maniekx86/M8SBC-486/pcb/cpu.kicad_sch

## KiCad design pcb/cpu.kicad_sch (2025-09-24)

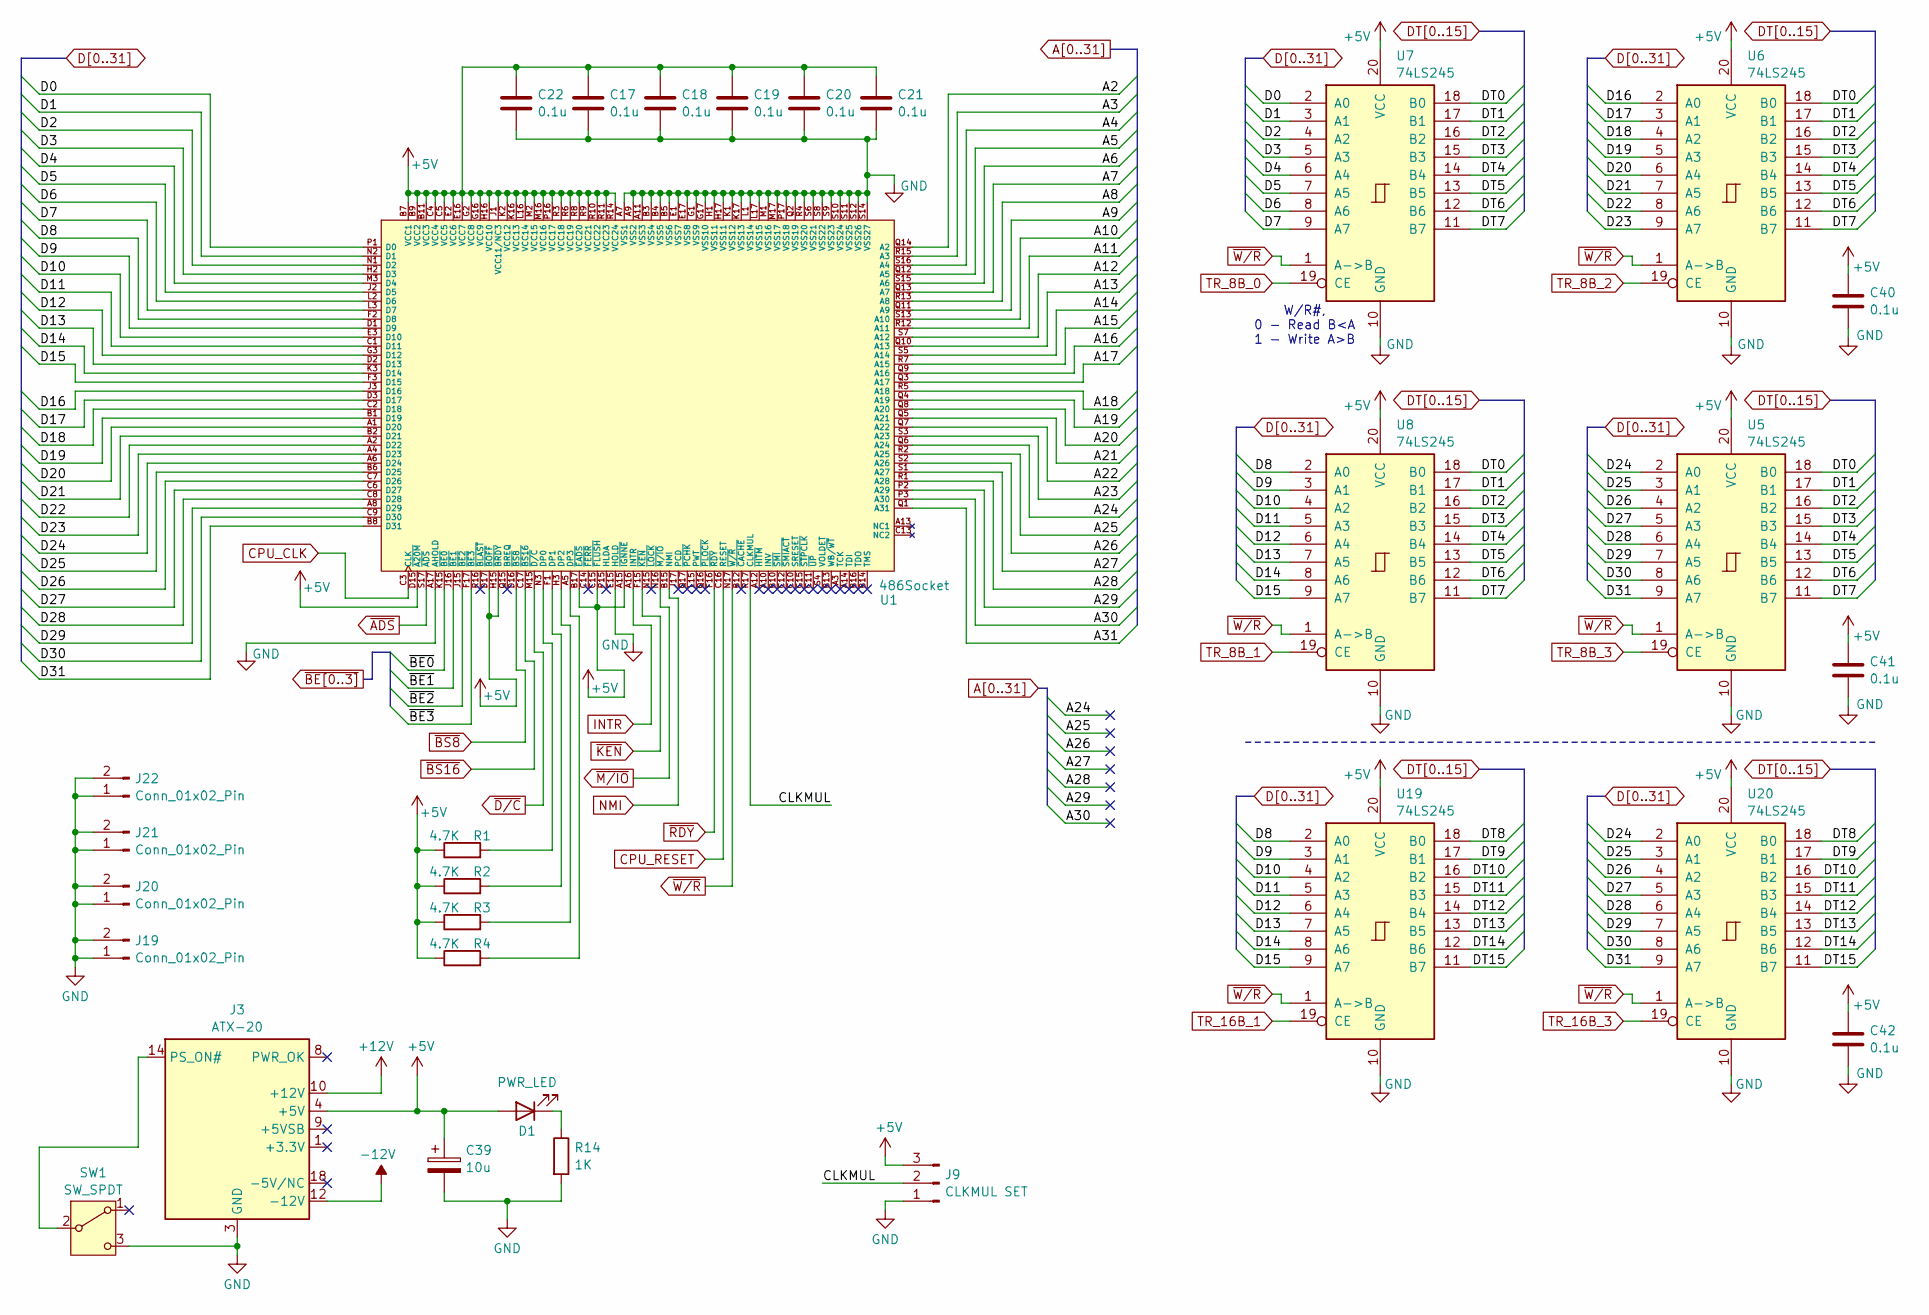
[picture p5: schematic cpu.kicad_sch]

Parts:
C17, C18, C19, C20, C21, C22, C40, C41, C42: 0.1u; C_0805_2012Metric_Pad1.18x1.45mm_HandSolder
C39: 10u; CP_Radial_D5.0mm_P2.50mm
D1: PWR_LED; LED_D4.0mm
J3: ATX-20; Molex_Mini-Fit_Jr_5566-20A_2x10_P4.20mm_Vertical
J9: CLKMUL SET; PinHeader_1x03_P2.54mm_Vertical
J19, J20, J21, J22: Conn_01x02_Pin; PinHeader_1x02_P2.54mm_Vertical
R1, R2, R3, R4: 4.7K; R_0805_2012Metric_Pad1.20x1.40mm_HandSolder
R14: 1K; R_0805_2012Metric_Pad1.20x1.40mm_HandSolder
SW1: SW_SPDT; PinHeader_1x03_P2.54mm_Vertical
U1: 486Socket
U5, U6, U7, U8, U19, U20: 74LS245; SOP-20_7.5x12.8mm_P1.27mm

Connections:
+5V: C17.2, C18.2, C19.2, C20.2, C21.2, C22.2, C39.1, C40.2, C41.2, C42.2, D1.2 (A), J3.4 (+5V), J3.6 (+5V), J3.19 (+5V), J3.20 (+5V), J9.3, R1.1, R2.1, R3.1, R4.1, U1.A15 (~IGNNE), U1.B7 (VCC1), U1.B9 (VCC2), U1.B11 (VCC3), U1.B17 (~EADS), U1.C4 (VCC4), U1.C5 (VCC5), U1.C15 (~FLUSH), U1.D15 (~A20M), U1.D17 (~BOFF), U1.E2 (VCC6), U1.E16 (VCC7), U1.G2 (VCC8), U1.G16 (VCC9), U1.H15 (~BRDY), U1.H16 (VCC10), U1.J1 (VCC11/NC3), U1.K2 (VCC12), U1.K16 (VCC13), U1.L16 (VCC14), U1.M2 (VCC15), U1.M16 (VCC16), U1.P16 (VCC17), U1.R3 (VCC18), U1.R6 (VCC19), U1.R8 (VCC20), U1.R9 (VCC21), U1.R10 (VCC22), U1.R11 (VCC23), U1.R14 (VCC24), U5.20 (VCC), U6.20 (VCC), U7.20 (VCC), U8.20 (VCC), U19.20 (VCC), U20.20 (VCC)
+12V: J3.10 (+12V)
-12V: J3.12 (-12V)
A2: U1.Q14 (A2)
A3: U1.R15 (A3)
A4: U1.S16 (A4)
A5: U1.Q12 (A5)
A6: U1.S15 (A6)
A7: U1.Q13 (A7)
A8: U1.R13 (A8)
A9: U1.Q11 (A9)
A10: U1.S13 (A10)
A11: U1.R12 (A11)
A12: U1.S7 (A12)
A13: U1.Q10 (A13)
A14: U1.S5 (A14)
A15: U1.R7 (A15)
A16: U1.Q9 (A16)
A17: U1.Q3 (A17)
A18: U1.R5 (A18)
A19: U1.Q4 (A19)
A20: U1.Q8 (A20)
A21: U1.Q5 (A21)
A22: U1.Q7 (A22)
A23: U1.S3 (A23)
A24: U1.Q6 (A24)
A25: U1.R2 (A25)
A26: U1.S2 (A26)
A27: U1.S1 (A27)
A28: U1.R1 (A28)
A29: U1.P2 (A29)
A30: U1.P3 (A30)
A31: U1.Q1 (A31)
CLKMUL: J9.2, U1.R17 (CLKMUL)
CPU_CLK: U1.C3 (CLK)
CPU_RESET: U1.C16 (RESET)
D0: U1.P1 (D0), U7.2 (A0)
D1: U1.N2 (D1), U7.3 (A1)
D2: U1.N1 (D2), U7.4 (A2)
D3: U1.H2 (D3), U7.5 (A3)
D4: U1.M3 (D4), U7.6 (A4)
D5: U1.J2 (D5), U7.7 (A5)
D6: U1.L2 (D6), U7.8 (A6)
D7: U1.L3 (D7), U7.9 (A7)
D8: U1.F2 (D8), U8.2 (A0), U19.2 (A0)
D9: U1.D1 (D9), U8.3 (A1), U19.3 (A1)
D10: U1.E3 (D10), U8.4 (A2), U19.4 (A2)
D11: U1.C1 (D11), U8.5 (A3), U19.5 (A3)
D12: U1.G3 (D12), U8.6 (A4), U19.6 (A4)
D13: U1.D2 (D13), U8.7 (A5), U19.7 (A5)
D14: U1.K3 (D14), U8.8 (A6), U19.8 (A6)
D15: U1.F3 (D15), U8.9 (A7), U19.9 (A7)
D16: U1.J3 (D16), U6.2 (A0)
D17: U1.D3 (D17), U6.3 (A1)
D18: U1.C2 (D18), U6.4 (A2)
D19: U1.B1 (D19), U6.5 (A3)
D20: U1.A1 (D20), U6.6 (A4)
D21: U1.B2 (D21), U6.7 (A5)
D22: U1.A2 (D22), U6.8 (A6)
D23: U1.A4 (D23), U6.9 (A7)
D24: U1.A6 (D24), U5.2 (A0), U20.2 (A0)
D25: U1.B6 (D25), U5.3 (A1), U20.3 (A1)
D26: U1.C7 (D26), U5.4 (A2), U20.4 (A2)
D27: U1.C6 (D27), U5.5 (A3), U20.5 (A3)
D28: U1.C8 (D28), U5.6 (A4), U20.6 (A4)
D29: U1.A8 (D29), U5.7 (A5), U20.7 (A5)
D30: U1.C9 (D30), U5.8 (A6), U20.8 (A6)
D31: U1.B8 (D31), U5.9 (A7), U20.9 (A7)
DT0: U5.18 (B0), U6.18 (B0), U7.18 (B0), U8.18 (B0)
DT1: U5.17 (B1), U6.17 (B1), U7.17 (B1), U8.17 (B1)
DT2: U5.16 (B2), U6.16 (B2), U7.16 (B2), U8.16 (B2)
DT3: U5.15 (B3), U6.15 (B3), U7.15 (B3), U8.15 (B3)
DT4: U5.14 (B4), U6.14 (B4), U7.14 (B4), U8.14 (B4)
DT5: U5.13 (B5), U6.13 (B5), U7.13 (B5), U8.13 (B5)
DT6: U5.12 (B6), U6.12 (B6), U7.12 (B6), U8.12 (B6)
DT7: U5.11 (B7), U6.11 (B7), U7.11 (B7), U8.11 (B7)
DT8: U19.18 (B0), U20.18 (B0)
DT9: U19.17 (B1), U20.17 (B1)
DT10: U19.16 (B2), U20.16 (B2)
DT11: U19.15 (B3), U20.15 (B3)
DT12: U19.14 (B4), U20.14 (B4)
DT13: U19.13 (B5), U20.13 (B5)
DT14: U19.12 (B6), U20.12 (B6)
DT15: U19.11 (B7), U20.11 (B7)
GND: C17.1, C18.1, C19.1, C20.1, C21.1, C22.1, C39.2, C40.1, C41.1, C42.1, J3.3 (GND), J3.5 (GND), J3.7 (GND), J3.13 (GND), J3.15 (GND), J3.16 (GND), J3.17 (GND), J9.1, J19.1, J19.2, J20.1, J20.2, J21.1, J21.2, J22.1, J22.2, R14.2, SW1.3 (C), U1.A7 (VSS1), U1.A9 (VSS2), U1.A11 (VSS3), U1.A17 (AHOLD), U1.B3 (VSS4), U1.B4 (VSS5), U1.B5 (VSS6), U1.E1 (VSS7), U1.E15 (HOLD), U1.E17 (VSS8), U1.G1 (VSS9), U1.G17 (VSS10), U1.H1 (VSS11), U1.H17 (VSS11), U1.K1 (VSS12), U1.K17 (VSS13), U1.L1 (VSS14), U1.L17 (VSS15), U1.M1 (VSS16), U1.M17 (VSS17), U1.P17 (VSS18), U1.Q2 (VSS19), U1.R4 (VSS20), U1.S6 (VSS21), U1.S8 (VSS22), U1.S9 (VSS23), U1.S10 (VSS24), U1.S11 (VSS25), U1.S12 (VSS26), U1.S14 (VSS27), U5.10 (GND), U6.10 (GND), U7.10 (GND), U8.10 (GND), U19.10 (GND), U20.10 (GND)
INTR: U1.A16 (INTR)
NMI: U1.B15 (NMI)
unnamed: D1.1 (K), R14.1
unnamed: J3.1 (+3.3V), J3.2 (+3.3V), J3.11 (+3.3V)
unnamed: J3.14 (PS_ON#), SW1.2 (B)
unnamed: R1.2, U1.N3 (DP0)
unnamed: R2.2, U1.F1 (DP1)
unnamed: R3.2, U1.H3 (DP2)
unnamed: R4.2, U1.A5 (DP3)
TR_8B_0: U7.19 (CE)
TR_8B_1: U8.19 (CE)
TR_8B_2: U6.19 (CE)
TR_8B_3: U5.19 (CE)
TR_16B_1: U19.19 (CE)
TR_16B_3: U20.19 (CE)
~ADS: U1.S17 (~ADS)
~BE0: U1.K15 (~BE0)
~BE1: U1.J16 (~BE1)
~BE2: U1.J15 (~BE2)
~BE3: U1.F17 (~BE3)
~BS8: U1.D16 (~BS8)
~BS16: U1.C17 (~BS16)
~D/C: U1.M15 (~D/C)
~KEN: U1.F15 (~KEN)
~M/IO: U1.N16 (~M/IO)
~RDY: U1.F16 (~RDY)
~W/R: U1.N17 (~W/R), U5.1 (A->B), U6.1 (A->B), U7.1 (A->B), U8.1 (A->B), U19.1 (A->B), U20.1 (A->B)

Notes on the sheet:
W/R#, 0 - Read B<A 1 - Write A>B
