maniekx86/M8SBC-486/pcb/fpga.kicad_sch

## KiCad design pcb/fpga.kicad_sch (2025-09-24)

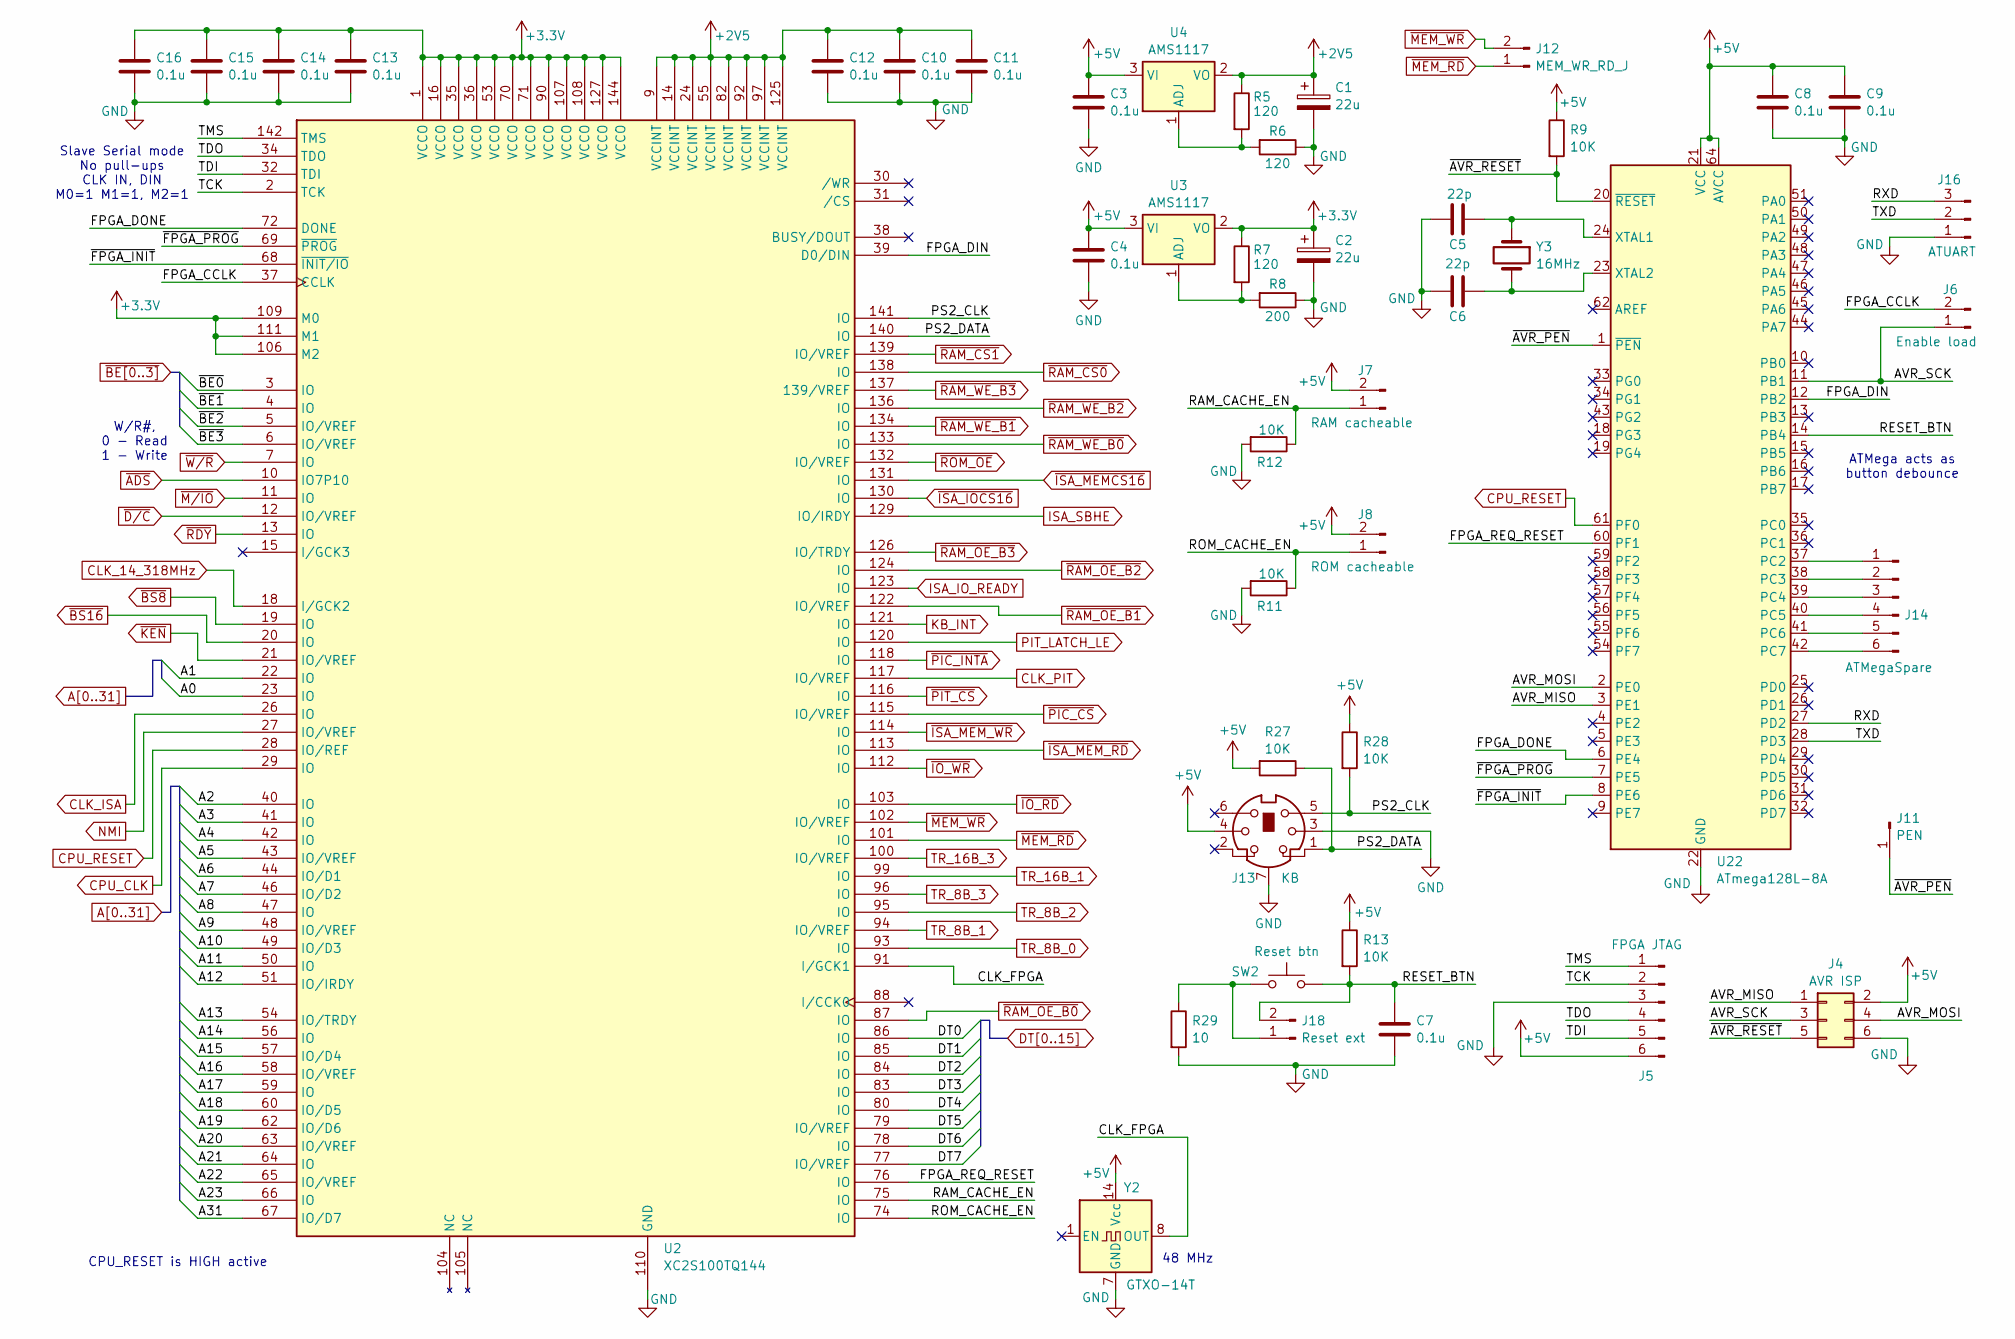
[picture p6: schematic fpga.kicad_sch]

Parts:
C1, C2: 22u; CP_Radial_D5.0mm_P2.50mm
C3, C4, C7, C8, C9, C10, C11, C12, C13, C14, C15, C16: 0.1u; C_0805_2012Metric_Pad1.18x1.45mm_HandSolder
C5, C6: 22p; C_0805_2012Metric_Pad1.18x1.45mm_HandSolder
J4: AVR ISP; PinHeader_2x03_P2.54mm_Vertical
J5: FPGA JTAG; PinHeader_1x06_P2.54mm_Vertical
J6: Enable load; PinHeader_1x02_P2.54mm_Vertical
J7: RAM cacheable; PinHeader_1x02_P2.54mm_Vertical
J8: ROM cacheable; PinHeader_1x02_P2.54mm_Vertical
J11: PEN; PinHeader_1x01_P2.54mm_Vertical
J12: MEM_WR_RD_J; PinHeader_1x02_P2.54mm_Vertical
J13: KB; Connector_Mini-DIN_Female_6Pin_2rows
J14: ATMegaSpare; PinHeader_1x06_P2.54mm_Vertical
J16: ATUART; PinHeader_1x03_P2.54mm_Vertical
J18: Reset ext; PinHeader_1x02_P2.54mm_Vertical
R5, R6, R7: 120; R_0805_2012Metric_Pad1.20x1.40mm_HandSolder
R8: 200; R_0805_2012Metric_Pad1.20x1.40mm_HandSolder
R9, R11, R12, R13, R27, R28: 10K; R_0805_2012Metric_Pad1.20x1.40mm_HandSolder
R29: 10; R_0805_2012Metric_Pad1.20x1.40mm_HandSolder
SW2: Reset btn; SW_PUSH_6mm
U2: XC2S100TQ144; TQFP-144_20x20mm_P0.5mm
U3, U4: AMS1117; SOT-223-3_TabPin2
U22: ATmega128L-8A; TQFP-64_14x14mm_P0.8mm
Y2: GTXO-14T; Oscillator_DIP-14
Y3: 16MHz; Crystal_HC49-4H_Vertical

Connections:
+2V5: C1.1, C10.2, C11.2, C12.2, R5.1, U2.9 (VCCINT), U2.14 (VCCINT), U2.24 (VCCINT), U2.55 (VCCINT), U2.82 (VCCINT), U2.92 (VCCINT), U2.97 (VCCINT), U2.125 (VCCINT), U4.2 (VO)
+3.3V: C2.1, C13.2, C14.2, C15.2, C16.2, R7.1, U2.1 (VCCO), U2.16 (VCCO), U2.35 (VCCO), U2.36 (VCCO), U2.53 (VCCO), U2.70 (VCCO), U2.71 (VCCO), U2.90 (VCCO), U2.106 (M2), U2.107 (VCCO), U2.108 (VCCO), U2.109 (M0), U2.111 (M1), U2.127 (VCCO), U2.144 (VCCO), U3.2 (VO)
+5V: C3.1, C4.1, C8.2, C9.2, J4.2, J5.6, J7.2, J8.2, J13.4, R9.1, R13.1, R27.2, R28.1, U3.3 (VI), U4.3 (VI), U22.21 (VCC), U22.52 (VCC), U22.64 (AVCC), Y2.14 (Vcc)
A0: U2.23 (IO)
A1: U2.22 (IO)
A2: U2.40 (IO)
A3: U2.41 (IO)
A4: U2.42 (IO)
A5: U2.43 (IO/VREF)
A6: U2.44 (IO/D1)
A7: U2.46 (IO/D2)
A8: U2.47 (IO)
A9: U2.48 (IO/VREF)
A10: U2.49 (IO/D3)
A11: U2.50 (IO)
A12: U2.51 (IO/IRDY)
A13: U2.54 (IO/TRDY)
A14: U2.56 (IO)
A15: U2.57 (IO/D4)
A16: U2.58 (IO/VREF)
A17: U2.59 (IO)
A18: U2.60 (IO/D5)
A19: U2.62 (IO/D6)
A20: U2.63 (IO/VREF)
A21: U2.64 (IO)
A22: U2.65 (IO/VREF)
A23: U2.66 (IO)
A31: U2.67 (IO/D7)
AVR_MISO: J4.1, U22.3 (PE1)
AVR_MOSI: J4.4, U22.2 (PE0)
AVR_SCK: J4.3, J6.1, U22.11 (PB1)
CLK_14_318MHz: U2.18 (I/GCK2)
CLK_FPGA: U2.91 (I/GCK1), Y2.8 (OUT)
CLK_ISA: U2.26 (IO)
CLK_PIT: U2.117 (IO/VREF)
CPU_CLK: U2.29 (IO)
CPU_RESET: U2.28 (IO/REF), U22.61 (PF0)
DT0: U2.86 (IO)
DT1: U2.85 (IO)
DT2: U2.84 (IO)
DT3: U2.83 (IO)
DT4: U2.80 (IO)
DT5: U2.79 (IO/VREF)
DT6: U2.78 (IO)
DT7: U2.77 (IO/VREF)
FPGA_CCLK: J6.2, U2.37 (CCLK)
FPGA_DIN: U2.39 (D0/DIN), U22.12 (PB2)
FPGA_DONE: U2.72 (DONE), U22.6 (PE4)
FPGA_REQ_RESET: U2.76 (IO), U22.60 (PF1)
GND: C1.2, C2.2, C3.2, C4.2, C5.1, C6.1, C7.2, C8.1, C9.1, C10.1, C11.1, C12.1, C13.1, C14.1, C15.1, C16.1, J4.6, J5.3, J13.3, J13.7, J16.1, R6.1, R8.1, R11.2, R12.2, R29.2, U2.8 (GND), U2.17 (GND), U2.25 (GND), U2.33 (GND), U2.45 (GND), U2.52 (GND), U2.61 (GND), U2.73 (GND), U2.81 (GND), U2.89 (GND), U2.98 (GND), U2.110 (GND), U2.119 (GND), U2.128 (GND), U2.135 (GND), U2.143 (GND), U22.22 (GND), U22.53 (GND), U22.63 (GND), Y2.7 (GND)
ISA_IO_READY: U2.123 (IO)
ISA_SBHE: U2.129 (IO/IRDY)
KB_INT: U2.121 (IO)
NMI: U2.27 (IO/VREF)
unnamed: C5.2, U22.24 (XTAL1), Y3.1
unnamed: C6.2, U22.23 (XTAL2), Y3.2
unnamed: J14.1, U22.37 (PC2)
unnamed: J14.2, U22.38 (PC3)
unnamed: J14.3, U22.39 (PC4)
unnamed: J14.4, U22.40 (PC5)
unnamed: J14.5, U22.41 (PC6)
unnamed: J14.6, U22.42 (PC7)
unnamed: J18.1, R29.1, SW2.1
unnamed: R5.2, R6.2, U4.1 (ADJ)
unnamed: R7.2, R8.2, U3.1 (ADJ)
PIT_LATCH_LE: U2.120 (IO)
PS2_CLK: J13.5, R28.2, U2.141 (IO)
PS2_DATA: J13.1, R27.1, U2.140 (IO)
RAM_CACHE_EN: J7.1, R12.1, U2.75 (IO)
RESET_BTN: C7.1, J18.2, R13.2, SW2.2, U22.14 (PB4)
ROM_CACHE_EN: J8.1, R11.1, U2.74 (IO)
RXD: J16.3, U22.27 (PD2)
TCK: J5.2, U2.2 (TCK)
TDI: J5.5, U2.32 (TDI)
TDO: J5.4, U2.34 (TDO)
TMS: J5.1, U2.142 (TMS)
TR_8B_0: U2.93 (IO)
TR_8B_1: U2.94 (IO/VREF)
TR_8B_2: U2.95 (IO)
TR_8B_3: U2.96 (IO)
TR_16B_1: U2.99 (IO)
TR_16B_3: U2.100 (IO/VREF)
TXD: J16.2, U22.28 (PD3)
~ADS: U2.10 (IO7P10)
~AVR_PEN: J11.1, U22.1 (~PEN)
~AVR_RESET: J4.5, R9.2, U22.20 (~RESET)
~BE0: U2.3 (IO)
~BE1: U2.4 (IO)
~BE2: U2.5 (IO/VREF)
~BE3: U2.6 (IO/VREF)
~BS8: U2.19 (IO)
~BS16: U2.20 (IO)
~D/C: U2.12 (IO/VREF)
~FPGA_INIT: U2.68 (~INIT/IO), U22.8 (PE6)
~FPGA_PROG: U2.69 (~PROG), U22.7 (PE5)
~IO_RD: U2.103 (IO)
~IO_WR: U2.112 (IO)
~ISA_IOCS16: U2.130 (IO)
~ISA_MEMCS16: U2.131 (IO)
~ISA_MEM_RD: U2.113 (IO)
~ISA_MEM_WR: U2.114 (IO)
~KEN: U2.21 (IO/VREF)
~MEM_RD: J12.1, U2.101 (IO)
~MEM_WR: J12.2, U2.102 (IO/VREF)
~M/IO: U2.11 (IO)
~PIC_CS: U2.115 (IO/VREF)
~PIC_INTA: U2.118 (IO)
~PIT_CS: U2.116 (IO)
~RAM_CS0: U2.138 (IO)
~RAM_CS1: U2.139 (IO/VREF)
~RAM_OE_B0: U2.87 (IO)
~RAM_OE_B1: U2.122 (IO/VREF)
~RAM_OE_B2: U2.124 (IO)
~RAM_OE_B3: U2.126 (IO/TRDY)
~RAM_WE_B0: U2.133 (IO)
~RAM_WE_B1: U2.134 (IO)
~RAM_WE_B2: U2.136 (IO)
~RAM_WE_B3: U2.137 (139/VREF)
~RDY: U2.13 (IO)
~ROM_OE: U2.132 (IO/VREF)
~W/R: U2.7 (IO)

Notes on the sheet:
CPU_RESET is HIGH active
Slave Serial mode No pull-ups CLK IN, DIN M0=1 M1=1, M2=1
ATMega acts as button debounce
48 MHz
W/R#, 0 - Read 1 - Write
