maniekx86/M8SBC-486/pcb/homebrew_486.kicad_sch

## KiCad design pcb/homebrew_486.kicad_sch (2025-09-24)

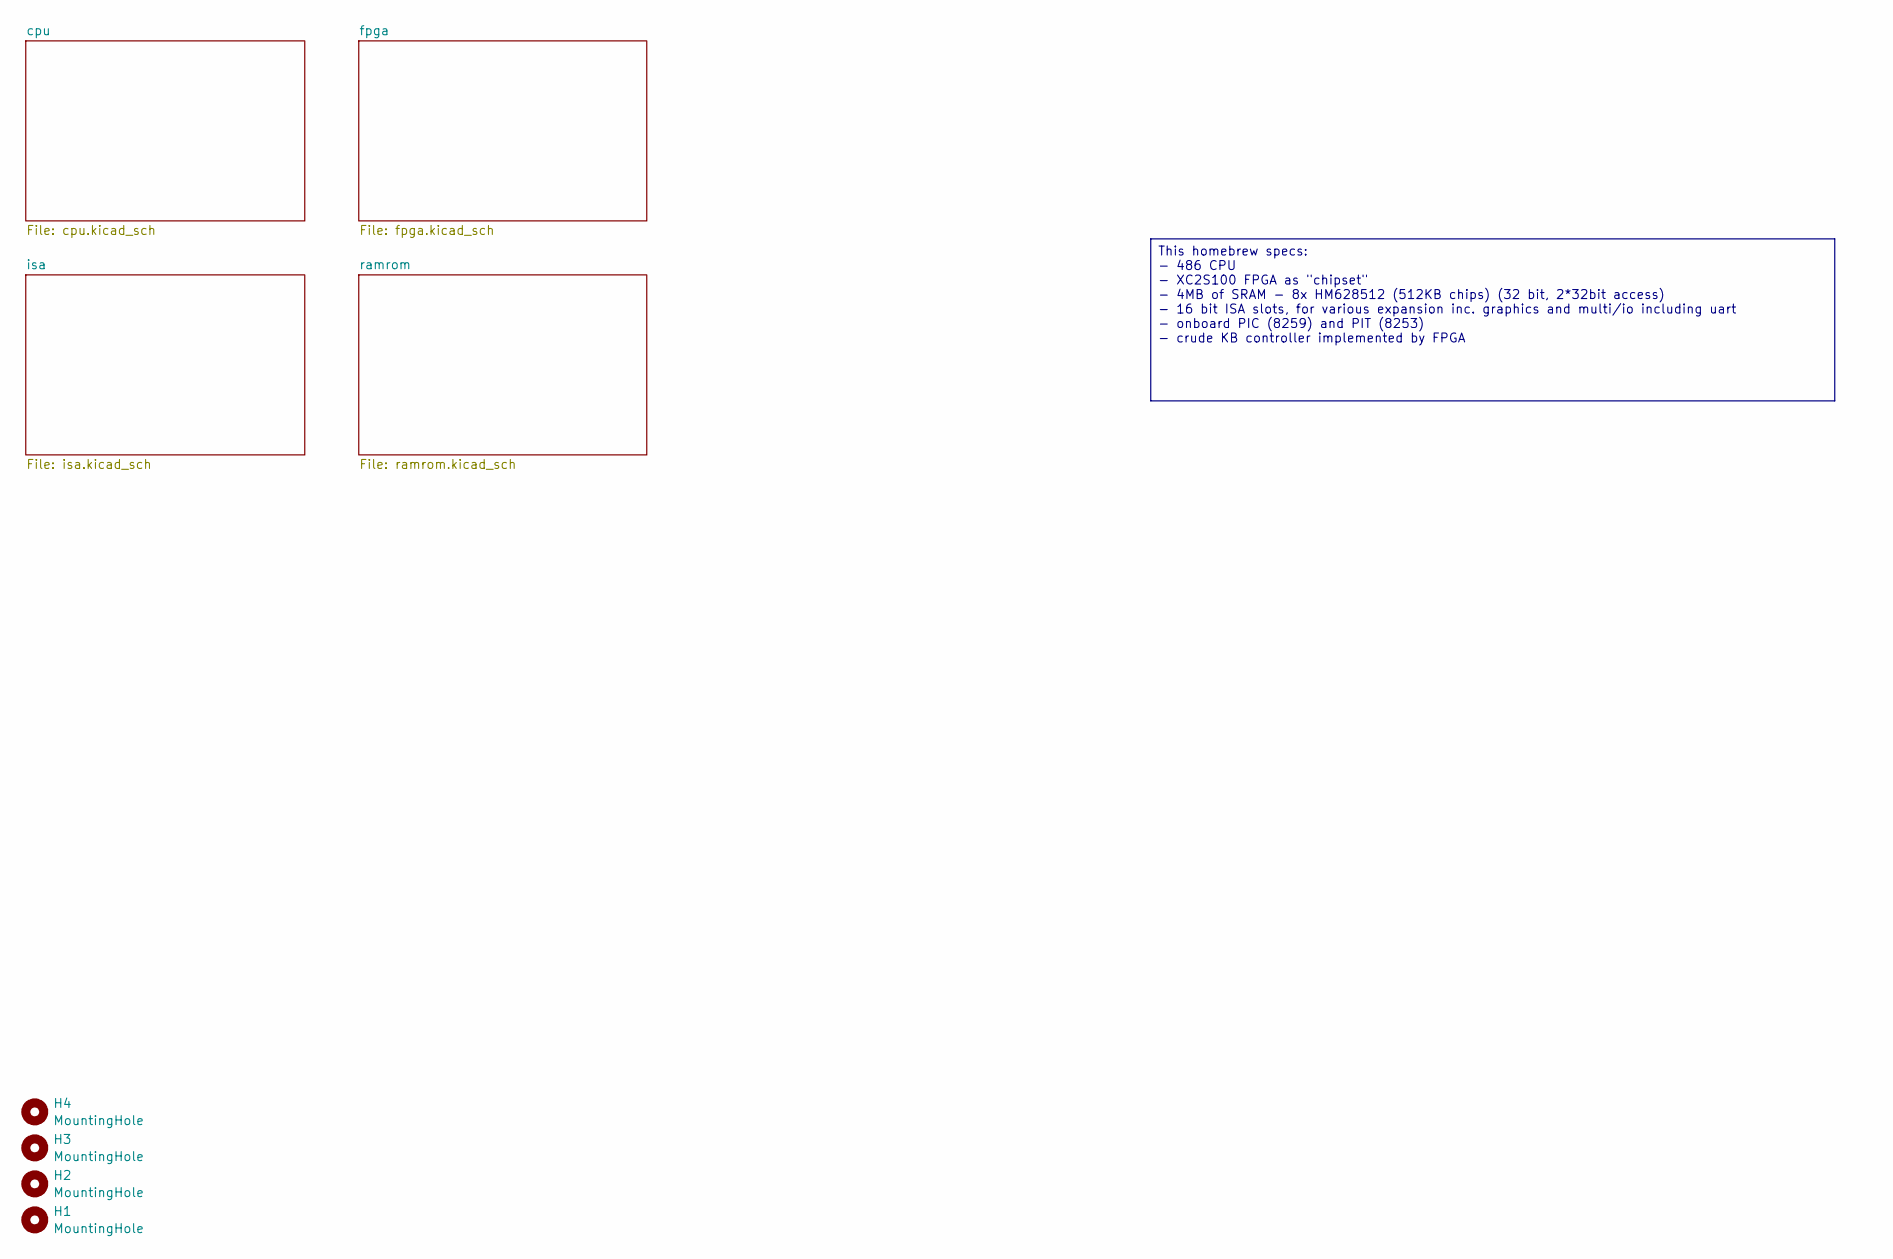
[picture p7: schematic homebrew_486.kicad_sch]

Parts:
H1, H2, H3, H4: MountingHole; MountingHole_4mm

Notes on the sheet:
This homebrew specs: - 486 CPU - XC2S100 FPGA as "chipset" - 4MB of SRAM - 8x HM628512 (512KB chips) (32 bit, 2*32bit access) - 16 bit ISA slots, for various expansion inc. graphics and multi/io including uart - onboard PIC (8259) and PIT (8253) - crude KB controller implemented by FPGA
