maniekx86/M8SBC-486/pcb/isa.kicad_sch

## KiCad design pcb/isa.kicad_sch (2025-09-24)

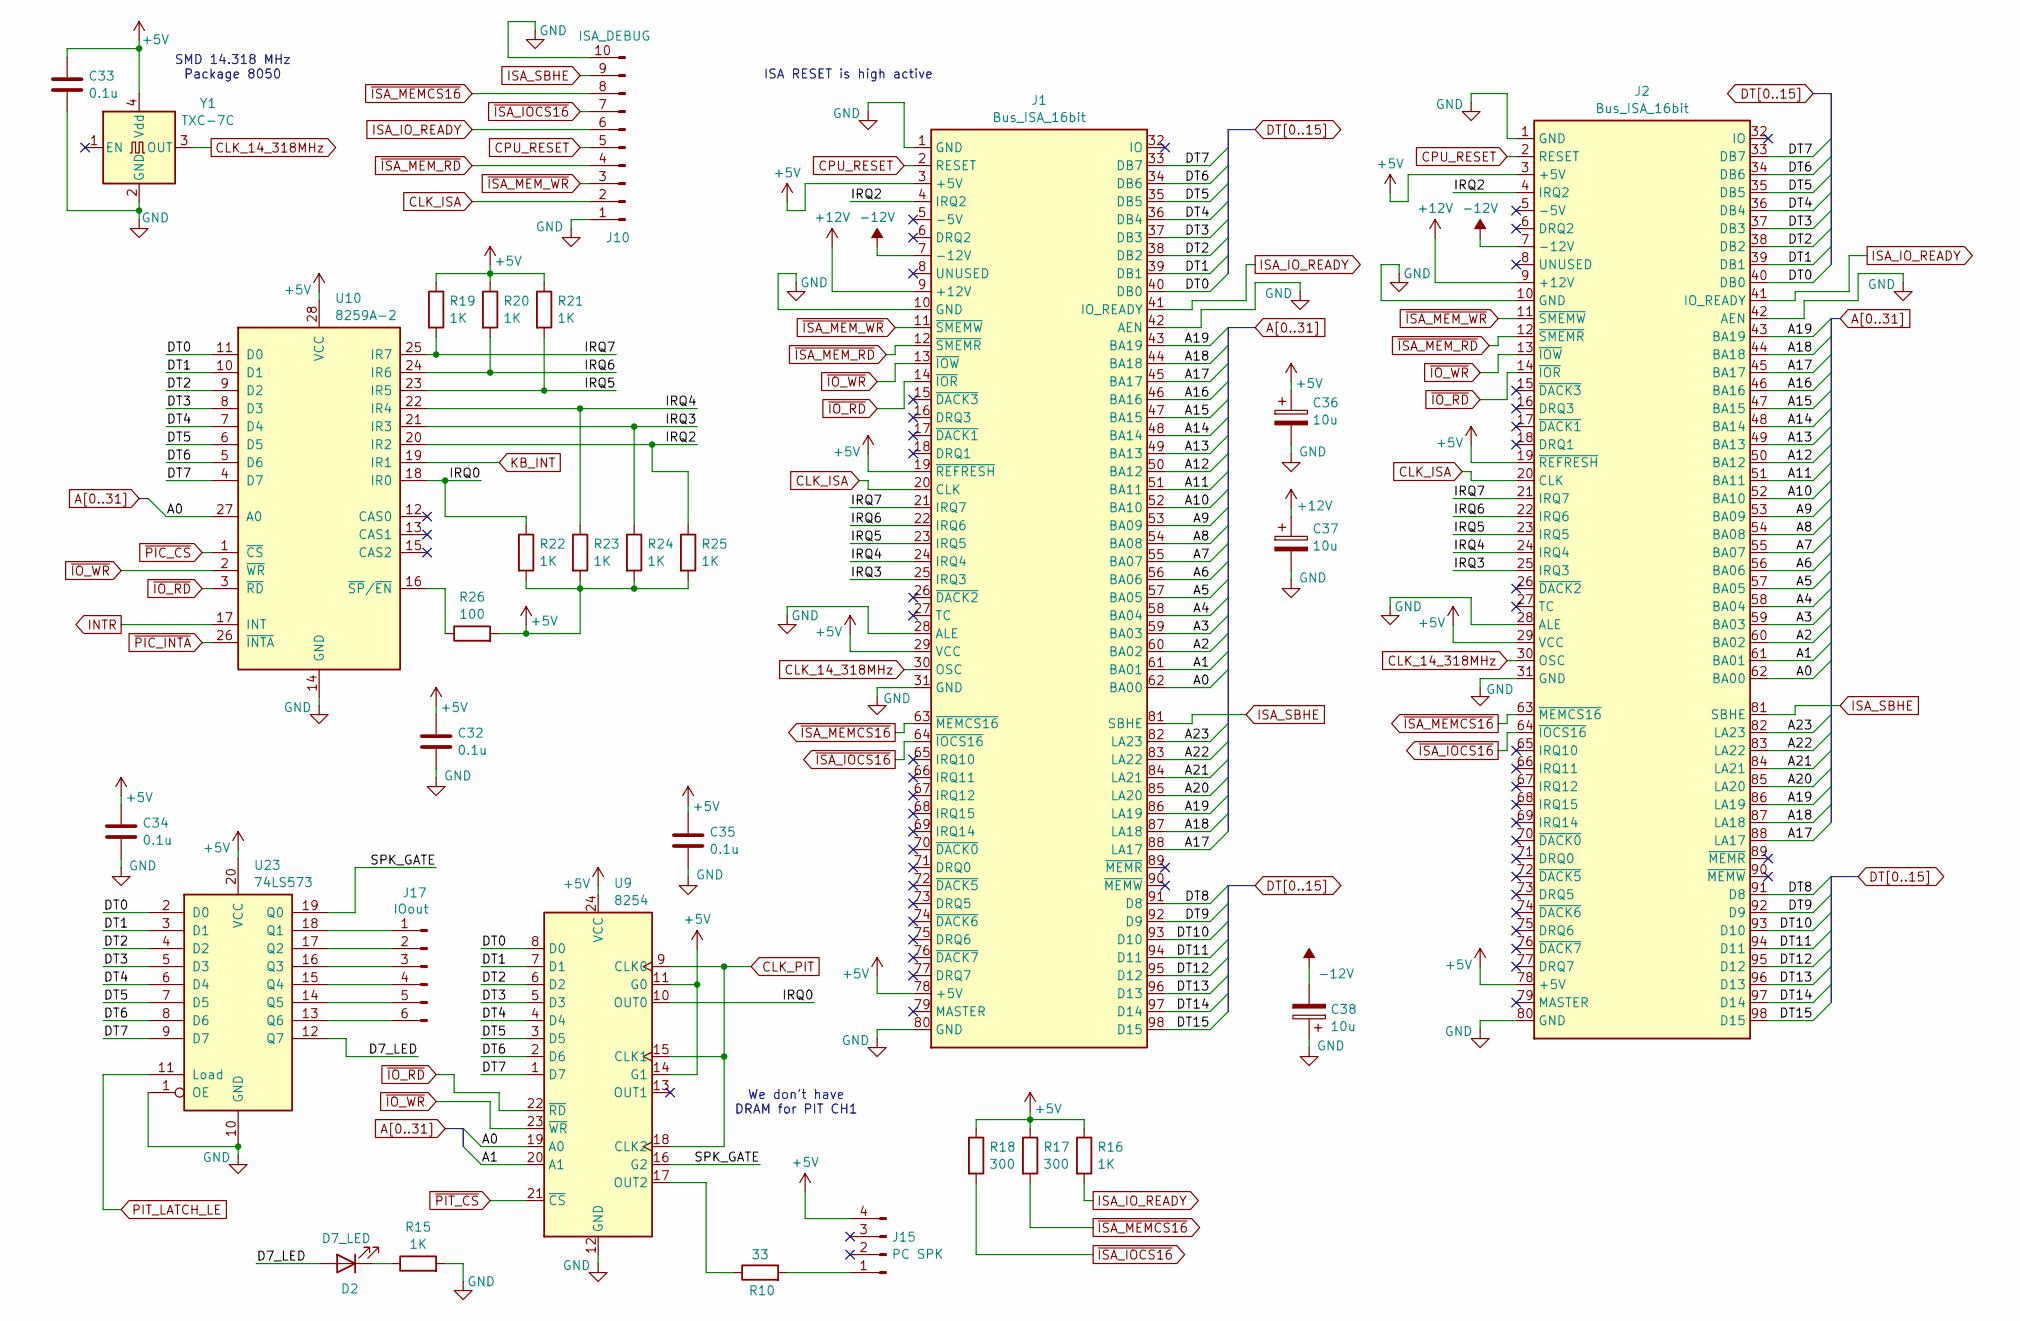
[picture p8: schematic isa.kicad_sch]

Parts:
C32, C33, C34, C35: 0.1u; C_0805_2012Metric_Pad1.18x1.45mm_HandSolder
C36, C37, C38: 10u; CP_Radial_D5.0mm_P2.50mm
D2: D7_LED; LED_D4.0mm
J1, J2: Bus_ISA_16bit; ISA16
J10: ISA_DEBUG; PinHeader_1x10_P2.54mm_Vertical
J15: PC SPK; PinHeader_1x04_P2.54mm_Vertical
J17: IOout; PinHeader_1x06_P2.54mm_Vertical
R10: 33; R_0805_2012Metric_Pad1.20x1.40mm_HandSolder
R15, R16, R19, R20, R21, R22, R23, R24, R25: 1K; R_0805_2012Metric_Pad1.20x1.40mm_HandSolder
R17, R18: 300; R_0805_2012Metric_Pad1.20x1.40mm_HandSolder
R26: 100; R_0805_2012Metric_Pad1.20x1.40mm_HandSolder
U9: 8254; DIP-24_W15.24mm
U10: 8259A-2; PLCC-28_THT-Socket
U23: 74LS573; SOP-20_7.5x12.8mm_P1.27mm
Y1: TXC-7C; Oscillator_SMD_SeikoEpson_SG8002CA-4Pin_7.0x5.0mm_HandSolde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

Connections:
+5V: C32.2, C33.2, C34.2, C35.2, C36.1, J1.3 (+5V), J1.19 (~REFRESH), J1.29 (VCC), J1.78 (+5V), J2.3 (+5V), J2.19 (~REFRESH), J2.29 (VCC), J2.78 (+5V), J15.4, R16.1, R17.1, R18.1, R19.1, R20.1, R21.1, R22.2, R23.2, R24.2, R25.2, R26.2, U9.11 (G0), U9.14 (G1), U9.24 (VCC), U10.28 (VCC), U23.20 (VCC), Y1.4 (Vdd)
+12V: C37.1, J1.9 (+12V), J2.9 (+12V)
-12V: C38.2, J1.7 (-12V), J2.7 (-12V)
A0: J1.62 (BA00), J2.62 (BA00), U9.19 (A0), U10.27 (A0)
A1: J1.61 (BA01), J2.61 (BA01), U9.20 (A1)
A2: J1.60 (BA02), J2.60 (BA02)
A3: J1.59 (BA03), J2.59 (BA03)
A4: J1.58 (BA04), J2.58 (BA04)
A5: J1.57 (BA05), J2.57 (BA05)
A6: J1.56 (BA06), J2.56 (BA06)
A7: J1.55 (BA07), J2.55 (BA07)
A8: J1.54 (BA08), J2.54 (BA08)
A9: J1.53 (BA09), J2.53 (BA09)
A10: J1.52 (BA10), J2.52 (BA10)
A11: J1.51 (BA11), J2.51 (BA11)
A12: J1.50 (BA12), J2.50 (BA12)
A13: J1.49 (BA13), J2.49 (BA13)
A14: J1.48 (BA14), J2.48 (BA14)
A15: J1.47 (BA15), J2.47 (BA15)
A16: J1.46 (BA16), J2.46 (BA16)
A17: J1.45 (BA17), J1.88 (LA17), J2.45 (BA17), J2.88 (LA17)
A18: J1.44 (BA18), J1.87 (LA18), J2.44 (BA18), J2.87 (LA18)
A19: J1.43 (BA19), J1.86 (LA19), J2.43 (BA19), J2.86 (LA19)
A20: J1.85 (LA20), J2.85 (LA20)
A21: J1.84 (LA21), J2.84 (LA21)
A22: J1.83 (LA22), J2.83 (LA22)
A23: J1.82 (LA23), J2.82 (LA23)
CLK_14_318MHz: J1.30 (OSC), J2.30 (OSC), Y1.3 (OUT)
CLK_ISA: J1.20 (CLK), J2.20 (CLK), J10.2
CLK_PIT: U9.9 (CLK0), U9.15 (CLK1), U9.18 (CLK2)
CPU_RESET: J1.2 (RESET), J2.2 (RESET), J10.5
D7_LED: D2.2 (A), U23.12 (Q7)
DT0: J1.40 (DB0), J2.40 (DB0), U9.8 (D0), U10.11 (D0), U23.2 (D0)
DT1: J1.39 (DB1), J2.39 (DB1), U9.7 (D1), U10.10 (D1), U23.3 (D1)
DT2: J1.38 (DB2), J2.38 (DB2), U9.6 (D2), U10.9 (D2), U23.4 (D2)
DT3: J1.37 (DB3), J2.37 (DB3), U9.5 (D3), U10.8 (D3), U23.5 (D3)
DT4: J1.36 (DB4), J2.36 (DB4), U9.4 (D4), U10.7 (D4), U23.6 (D4)
DT5: J1.35 (DB5), J2.35 (DB5), U9.3 (D5), U10.6 (D5), U23.7 (D5)
DT6: J1.34 (DB6), J2.34 (DB6), U9.2 (D6), U10.5 (D6), U23.8 (D6)
DT7: J1.33 (DB7), J2.33 (DB7), U9.1 (D7), U10.4 (D7), U23.9 (D7)
DT8: J1.91 (D8), J2.91 (D8)
DT9: J1.92 (D9), J2.92 (D9)
DT10: J1.93 (D10), J2.93 (D10)
DT11: J1.94 (D11), J2.94 (D11)
DT12: J1.95 (D12), J2.95 (D12)
DT13: J1.96 (D13), J2.96 (D13)
DT14: J1.97 (D14), J2.97 (D14)
DT15: J1.98 (D15), J2.98 (D15)
GND: C32.1, C33.1, C34.1, C35.1, C36.2, C37.2, C38.1, J1.1 (GND), J1.10 (GND), J1.28 (ALE), J1.31 (GND), J1.42 (AEN), J1.80 (GND), J2.1 (GND), J2.10 (GND), J2.28 (ALE), J2.31 (GND), J2.42 (AEN), J2.80 (GND), J10.1, J10.10, R15.2, U9.12 (GND), U10.14 (GND), U23.1 (OE), U23.10 (GND), Y1.2 (GND)
INTR: U10.17 (INT)
IRQ0: R22.1, U9.10 (OUT0), U10.18 (IR0)
IRQ2: J1.4 (IRQ2), J2.4 (IRQ2), R25.1, U10.20 (IR2)
IRQ3: J1.25 (IRQ3), J2.25 (IRQ3), R24.1, U10.21 (IR3)
IRQ4: J1.24 (IRQ4), J2.24 (IRQ4), R23.1, U10.22 (IR4)
IRQ5: J1.23 (IRQ5), J2.23 (IRQ5), R21.2, U10.23 (IR5)
IRQ6: J1.22 (IRQ6), J2.22 (IRQ6), R20.2, U10.24 (IR6)
IRQ7: J1.21 (IRQ7), J2.21 (IRQ7), R19.2, U10.25 (IR7)
ISA_IO_READY: J1.41 (IO_READY), J2.41 (IO_READY), J10.6, R16.2
ISA_SBHE: J1.81 (SBHE), J2.81 (SBHE), J10.9
KB_INT: U10.19 (IR1)
unnamed: D2.1 (K), R15.1
unnamed: J15.1, R10.2
unnamed: J17.1, U23.18 (Q1)
unnamed: J17.2, U23.17 (Q2)
unnamed: J17.3, U23.16 (Q3)
unnamed: J17.4, U23.15 (Q4)
unnamed: J17.5, U23.14 (Q5)
unnamed: J17.6, U23.13 (Q6)
unnamed: R10.1, U9.17 (OUT2)
unnamed: R26.1, U10.16 (~SP/~EN)
PIT_LATCH_LE: U23.11 (Load)
SPK_GATE: U9.16 (G2), U23.19 (Q0)
~IO_RD: J1.14 (~IOR), J2.14 (~IOR), U9.22 (~RD), U10.3 (~RD)
~IO_WR: J1.13 (~IOW), J2.13 (~IOW), U9.23 (~WR), U10.2 (~WR)
~ISA_IOCS16: J1.64 (~IOCS16), J2.64 (~IOCS16), J10.7, R18.2
~ISA_MEMCS16: J1.63 (~MEMCS16), J2.63 (~MEMCS16), J10.8, R17.2
~ISA_MEM_RD: J1.12 (~SMEMR), J2.12 (~SMEMR), J10.4
~ISA_MEM_WR: J1.11 (~SMEMW), J2.11 (~SMEMW), J10.3
~PIC_CS: U10.1 (~CS)
~PIC_INTA: U10.26 (~INTA)
~PIT_CS: U9.21 (~CS)

Notes on the sheet:
We don't have DRAM for PIT CH1
SMD 14.318 MHz Package 8050
ISA RESET is high active
