maniekx86/M8SBC-486/pcb/ramrom.kicad_sch

## KiCad design pcb/ramrom.kicad_sch (2025-09-24)

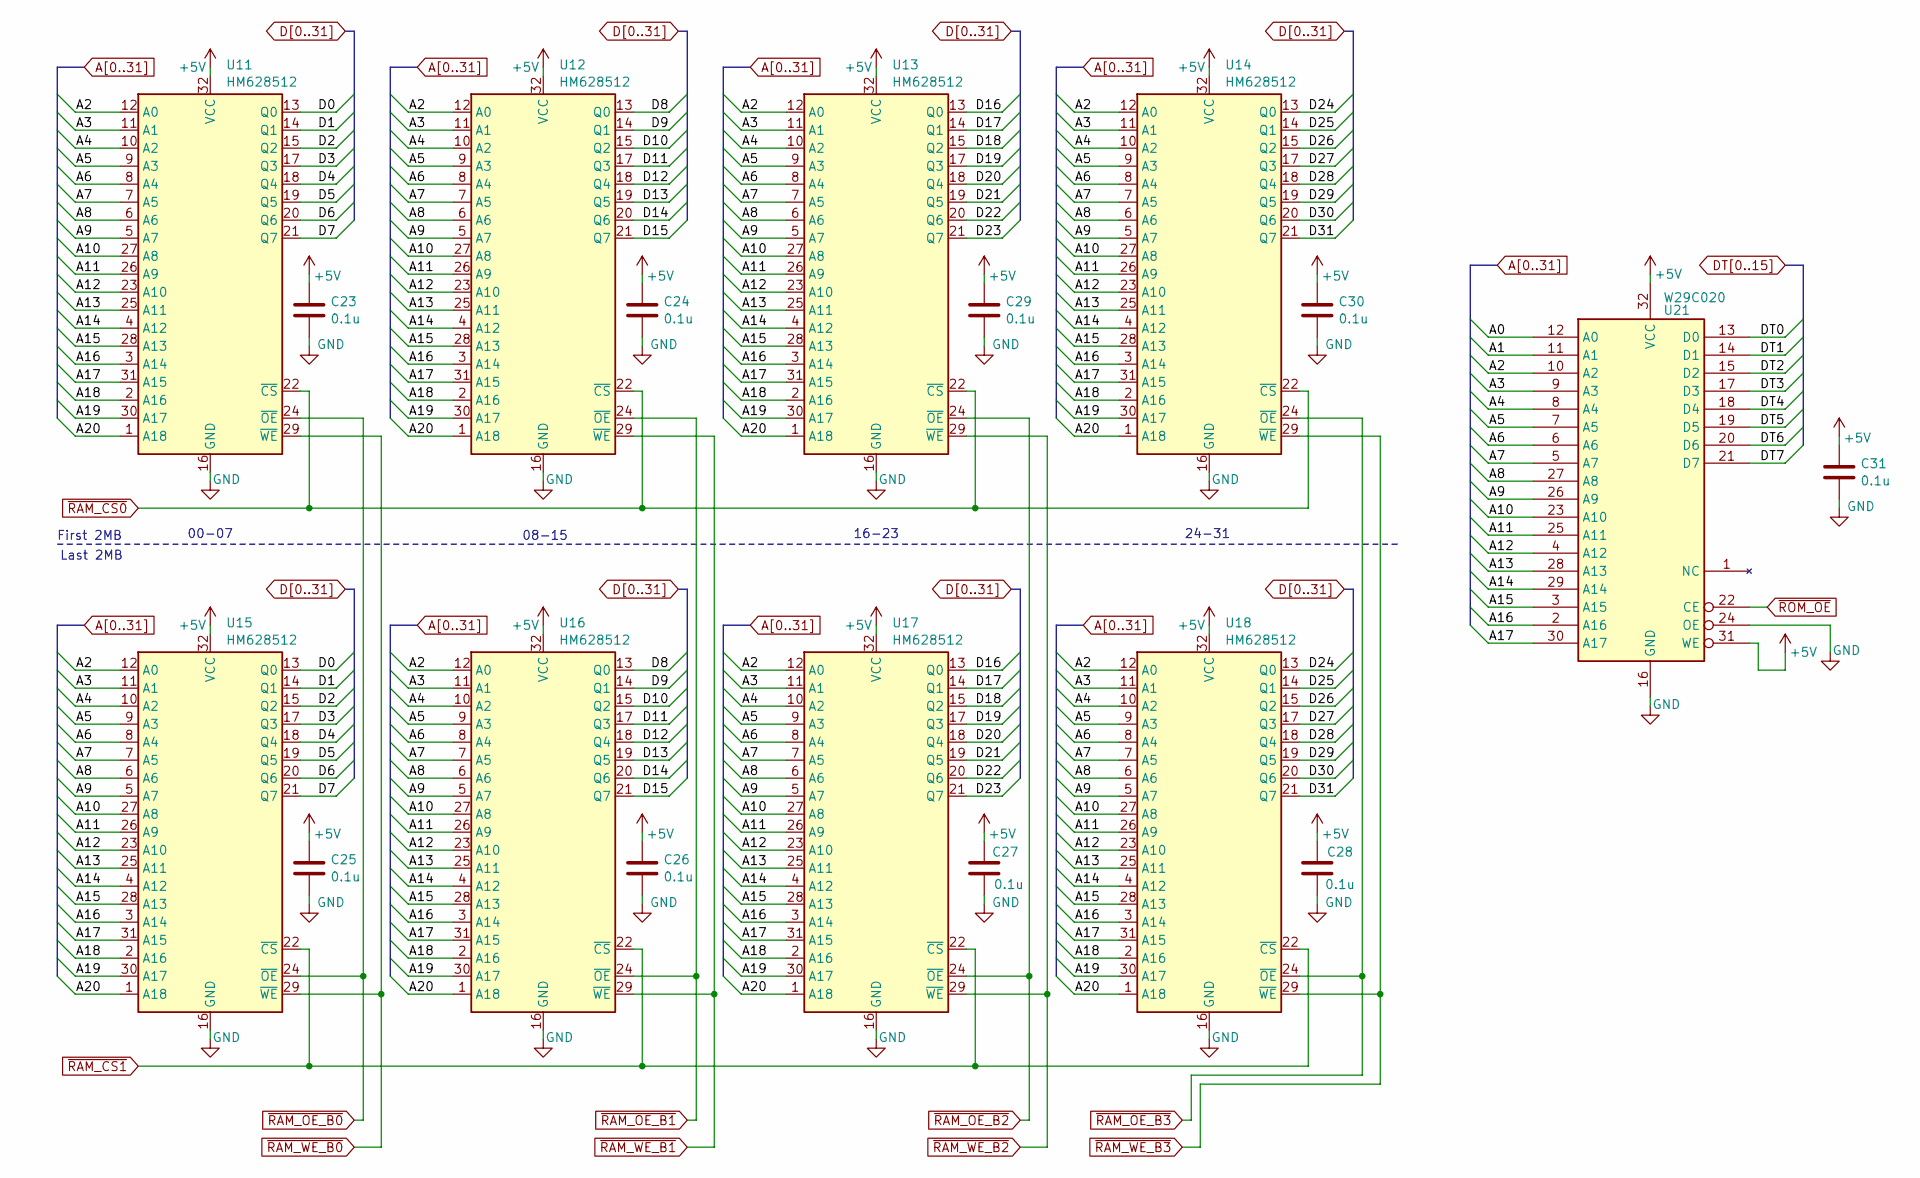
[picture p9: schematic ramrom.kicad_sch]

Parts:
C23, C24, C25, C26, C27, C28, C29, C30, C31: 0.1u; C_0805_2012Metric_Pad1.18x1.45mm_HandSolder
U11, U12, U13, U14, U15, U16, U17, U18: HM628512; SOP-32_11.305x20.495mm_P1.27mm
U21: W29C020; DIP-32_W15.24mm

Connections:
+5V: C23.2, C24.2, C25.2, C26.2, C27.2, C28.2, C29.2, C30.2, C31.2, U11.32 (VCC), U12.32 (VCC), U13.32 (VCC), U14.32 (VCC), U15.32 (VCC), U16.32 (VCC), U17.32 (VCC), U18.32 (VCC), U21.31 (WE), U21.32 (VCC)
A0: U21.12 (A0)
A1: U21.11 (A1)
A2: U11.12 (A0), U12.12 (A0), U13.12 (A0), U14.12 (A0), U15.12 (A0), U16.12 (A0), U17.12 (A0), U18.12 (A0), U21.10 (A2)
A3: U11.11 (A1), U12.11 (A1), U13.11 (A1), U14.11 (A1), U15.11 (A1), U16.11 (A1), U17.11 (A1), U18.11 (A1), U21.9 (A3)
A4: U11.10 (A2), U12.10 (A2), U13.10 (A2), U14.10 (A2), U15.10 (A2), U16.10 (A2), U17.10 (A2), U18.10 (A2), U21.8 (A4)
A5: U11.9 (A3), U12.9 (A3), U13.9 (A3), U14.9 (A3), U15.9 (A3), U16.9 (A3), U17.9 (A3), U18.9 (A3), U21.7 (A5)
A6: U11.8 (A4), U12.8 (A4), U13.8 (A4), U14.8 (A4), U15.8 (A4), U16.8 (A4), U17.8 (A4), U18.8 (A4), U21.6 (A6)
A7: U11.7 (A5), U12.7 (A5), U13.7 (A5), U14.7 (A5), U15.7 (A5), U16.7 (A5), U17.7 (A5), U18.7 (A5), U21.5 (A7)
A8: U11.6 (A6), U12.6 (A6), U13.6 (A6), U14.6 (A6), U15.6 (A6), U16.6 (A6), U17.6 (A6), U18.6 (A6), U21.27 (A8)
A9: U11.5 (A7), U12.5 (A7), U13.5 (A7), U14.5 (A7), U15.5 (A7), U16.5 (A7), U17.5 (A7), U18.5 (A7), U21.26 (A9)
A10: U11.27 (A8), U12.27 (A8), U13.27 (A8), U14.27 (A8), U15.27 (A8), U16.27 (A8), U17.27 (A8), U18.27 (A8), U21.23 (A10)
A11: U11.26 (A9), U12.26 (A9), U13.26 (A9), U14.26 (A9), U15.26 (A9), U16.26 (A9), U17.26 (A9), U18.26 (A9), U21.25 (A11)
A12: U11.23 (A10), U12.23 (A10), U13.23 (A10), U14.23 (A10), U15.23 (A10), U16.23 (A10), U17.23 (A10), U18.23 (A10), U21.4 (A12)
A13: U11.25 (A11), U12.25 (A11), U13.25 (A11), U14.25 (A11), U15.25 (A11), U16.25 (A11), U17.25 (A11), U18.25 (A11), U21.28 (A13)
A14: U11.4 (A12), U12.4 (A12), U13.4 (A12), U14.4 (A12), U15.4 (A12), U16.4 (A12), U17.4 (A12), U18.4 (A12), U21.29 (A14)
A15: U11.28 (A13), U12.28 (A13), U13.28 (A13), U14.28 (A13), U15.28 (A13), U16.28 (A13), U17.28 (A13), U18.28 (A13), U21.3 (A15)
A16: U11.3 (A14), U12.3 (A14), U13.3 (A14), U14.3 (A14), U15.3 (A14), U16.3 (A14), U17.3 (A14), U18.3 (A14), U21.2 (A16)
A17: U11.31 (A15), U12.31 (A15), U13.31 (A15), U14.31 (A15), U15.31 (A15), U16.31 (A15), U17.31 (A15), U18.31 (A15), U21.30 (A17)
A18: U11.2 (A16), U12.2 (A16), U13.2 (A16), U14.2 (A16), U15.2 (A16), U16.2 (A16), U17.2 (A16), U18.2 (A16)
A19: U11.30 (A17), U12.30 (A17), U13.30 (A17), U14.30 (A17), U15.30 (A17), U16.30 (A17), U17.30 (A17), U18.30 (A17)
A20: U11.1 (A18), U12.1 (A18), U13.1 (A18), U14.1 (A18), U15.1 (A18), U16.1 (A18), U17.1 (A18), U18.1 (A18)
D0: U11.13 (Q0), U15.13 (Q0)
D1: U11.14 (Q1), U15.14 (Q1)
D2: U11.15 (Q2), U15.15 (Q2)
D3: U11.17 (Q3), U15.17 (Q3)
D4: U11.18 (Q4), U15.18 (Q4)
D5: U11.19 (Q5), U15.19 (Q5)
D6: U11.20 (Q6), U15.20 (Q6)
D7: U11.21 (Q7), U15.21 (Q7)
D8: U12.13 (Q0), U16.13 (Q0)
D9: U12.14 (Q1), U16.14 (Q1)
D10: U12.15 (Q2), U16.15 (Q2)
D11: U12.17 (Q3), U16.17 (Q3)
D12: U12.18 (Q4), U16.18 (Q4)
D13: U12.19 (Q5), U16.19 (Q5)
D14: U12.20 (Q6), U16.20 (Q6)
D15: U12.21 (Q7), U16.21 (Q7)
D16: U13.13 (Q0), U17.13 (Q0)
D17: U13.14 (Q1), U17.14 (Q1)
D18: U13.15 (Q2), U17.15 (Q2)
D19: U13.17 (Q3), U17.17 (Q3)
D20: U13.18 (Q4), U17.18 (Q4)
D21: U13.19 (Q5), U17.19 (Q5)
D22: U13.20 (Q6), U17.20 (Q6)
D23: U13.21 (Q7), U17.21 (Q7)
D24: U14.13 (Q0), U18.13 (Q0)
D25: U14.14 (Q1), U18.14 (Q1)
D26: U14.15 (Q2), U18.15 (Q2)
D27: U14.17 (Q3), U18.17 (Q3)
D28: U14.18 (Q4), U18.18 (Q4)
D29: U14.19 (Q5), U18.19 (Q5)
D30: U14.20 (Q6), U18.20 (Q6)
D31: U14.21 (Q7), U18.21 (Q7)
DT0: U21.13 (D0)
DT1: U21.14 (D1)
DT2: U21.15 (D2)
DT3: U21.17 (D3)
DT4: U21.18 (D4)
DT5: U21.19 (D5)
DT6: U21.20 (D6)
DT7: U21.21 (D7)
GND: C23.1, C24.1, C25.1, C26.1, C27.1, C28.1, C29.1, C30.1, C31.1, U11.16 (GND), U12.16 (GND), U13.16 (GND), U14.16 (GND), U15.16 (GND), U16.16 (GND), U17.16 (GND), U18.16 (GND), U21.16 (GND), U21.24 (OE)
~RAM_CS0: U11.22 (~CS), U12.22 (~CS), U13.22 (~CS), U14.22 (~CS)
~RAM_CS1: U15.22 (~CS), U16.22 (~CS), U17.22 (~CS), U18.22 (~CS)
~RAM_OE_B0: U11.24 (~OE), U15.24 (~OE)
~RAM_OE_B1: U12.24 (~OE), U16.24 (~OE)
~RAM_OE_B2: U13.24 (~OE), U17.24 (~OE)
~RAM_OE_B3: U14.24 (~OE), U18.24 (~OE)
~RAM_WE_B0: U11.29 (~WE), U15.29 (~WE)
~RAM_WE_B1: U12.29 (~WE), U16.29 (~WE)
~RAM_WE_B2: U13.29 (~WE), U17.29 (~WE)
~RAM_WE_B3: U14.29 (~WE), U18.29 (~WE)
~ROM_OE: U21.22 (CE)

Notes on the sheet:
16-23
First 2MB
00-07
24-31
08-15
Last 2MB
